kkunzelm/simpleTempLogger/images/sensor-armada.jpg

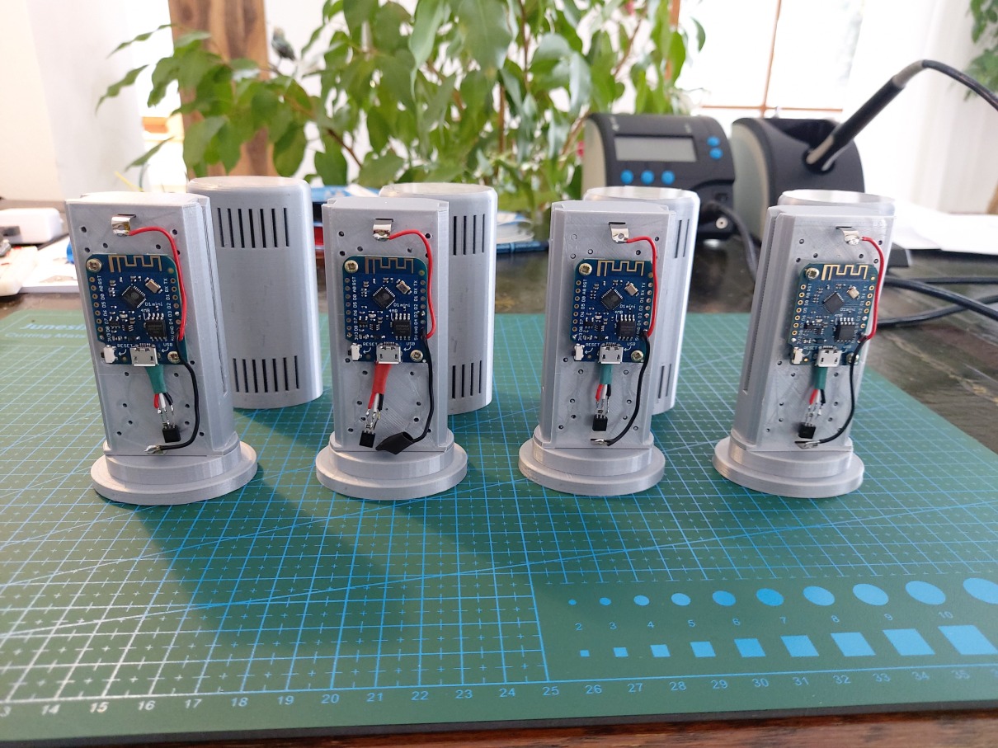
images/sensor-armada.jpg
