kkunzelm/simpleTempLogger/images/smd-pullup-resistor.jpg

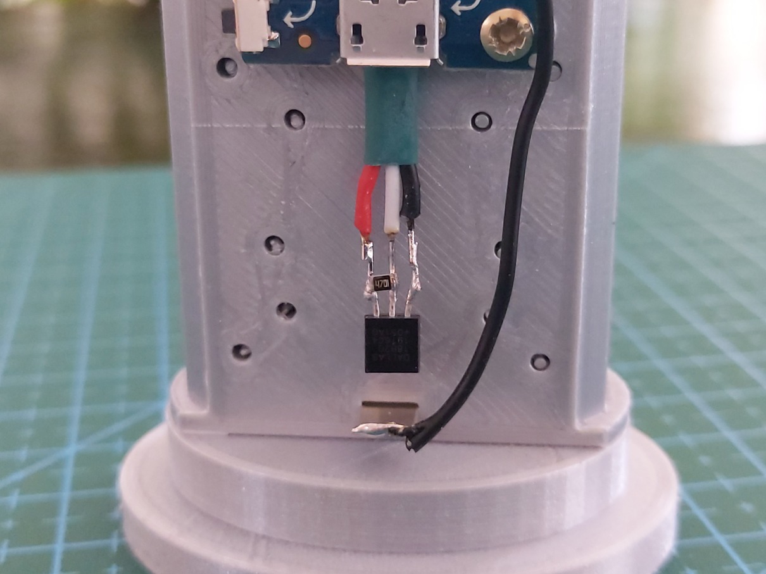
images/smd-pullup-resistor.jpg
